DziekiTeknomanci/EyeshieldPress/Photos/DSCF0188.jpg

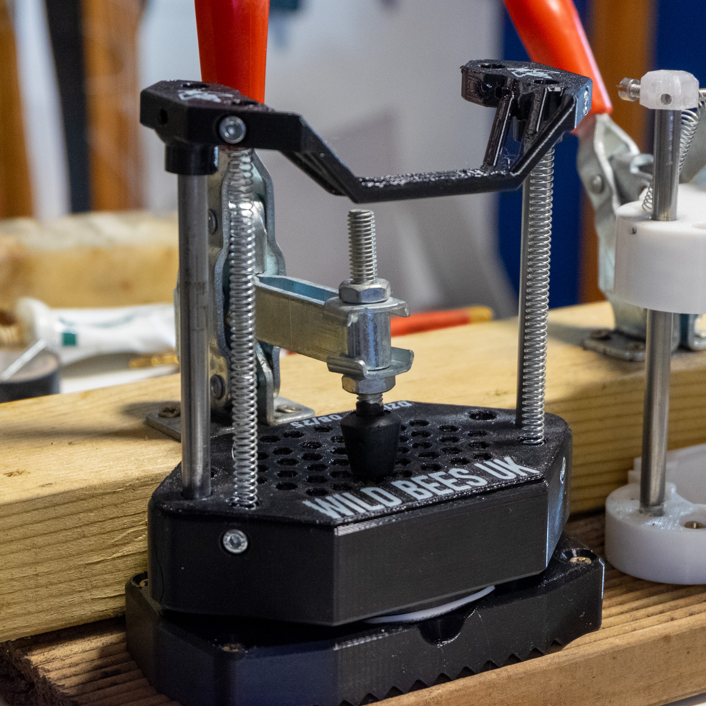
Photos/DSCF0188.jpg
