DziekiTeknomanci/EyeshieldPress/Photos/DSCF0193.jpg

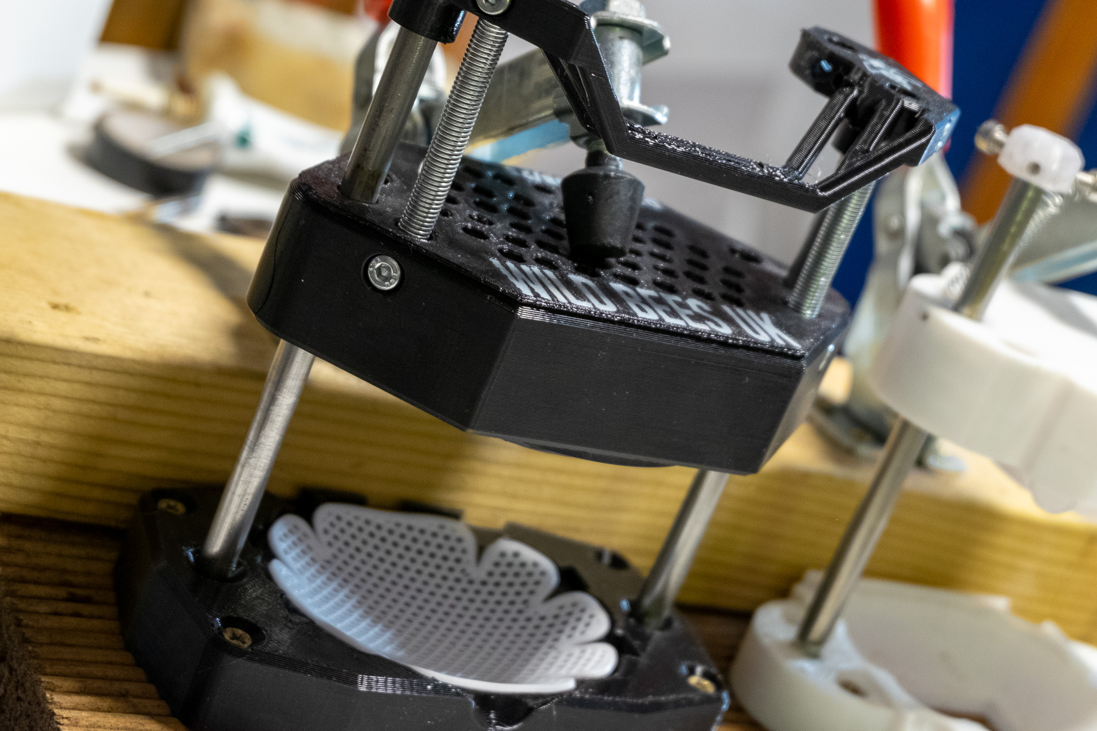
Photos/DSCF0193.jpg
