DziekiTeknomanci/EyeshieldPress/Photos/DSCF0202.jpg

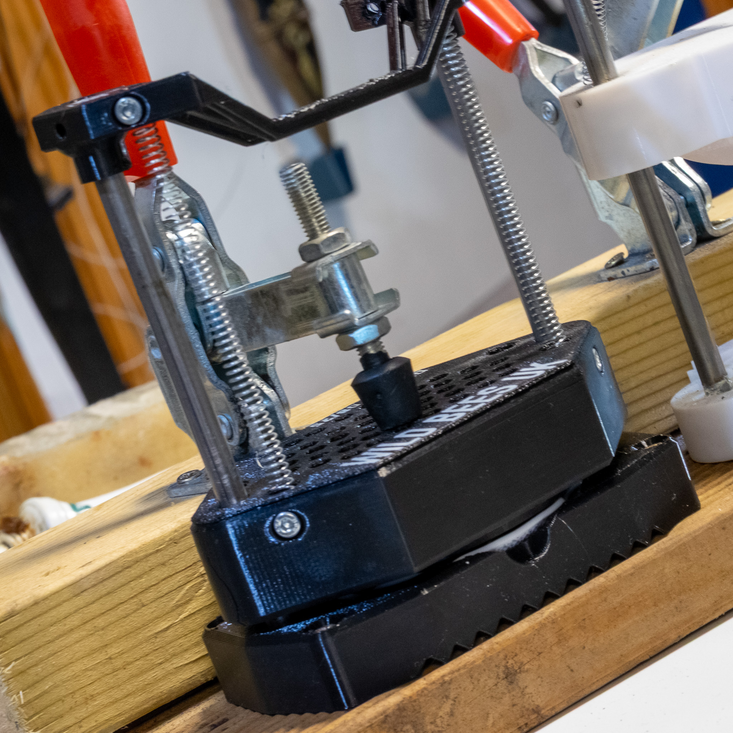
Photos/DSCF0202.jpg
